ayarimatsui/Portable_Drinkbar/raspi-case-CAD/base_of_base.SLDPRT

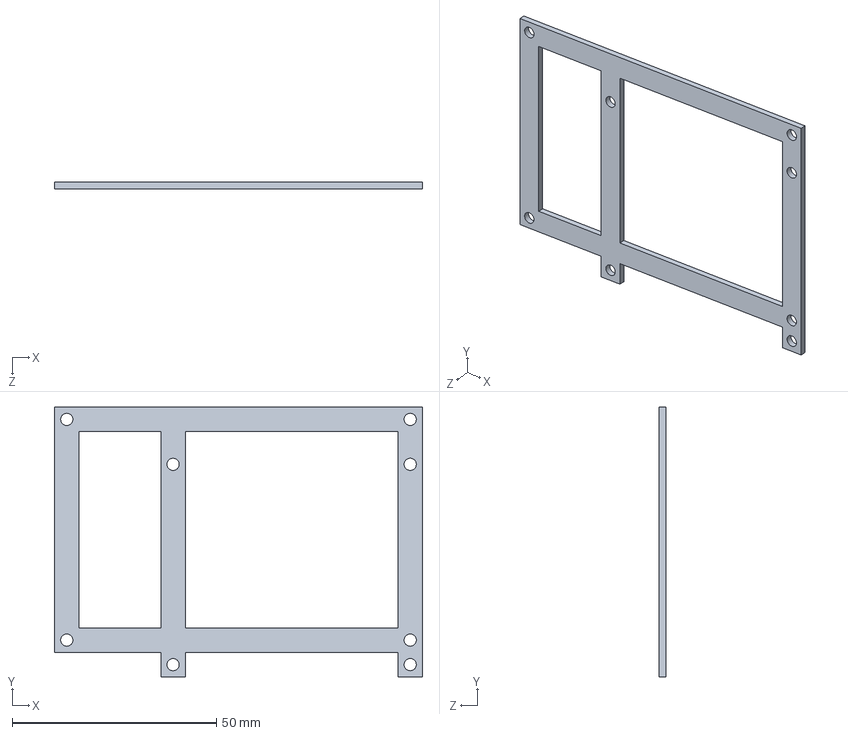
[picture p26: CAD file, 2020-01-28]
raspi-case-CAD/base_of_base.SLDPRT
90.0 x 66.0 x 1.60 mm
