ayarimatsui/Portable_Drinkbar/make_aroma/CAD_data/aroma-maker-CAD/cover/parts/cover_top.SLDPRT

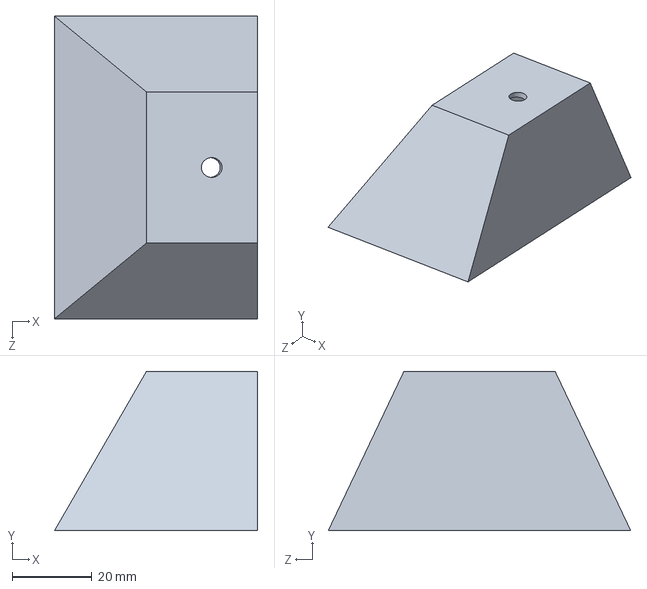
[picture p27: CAD file, 2019-12-03]
make_aroma/CAD_data/aroma-maker-CAD/cover/parts/cover_top.SLDPRT
51.0 x 40.0 x 76.0 mm
