ayarimatsui/Portable_Drinkbar/make_aroma/CAD_data/aroma-maker-CAD/main/parts/pin.SLDPRT

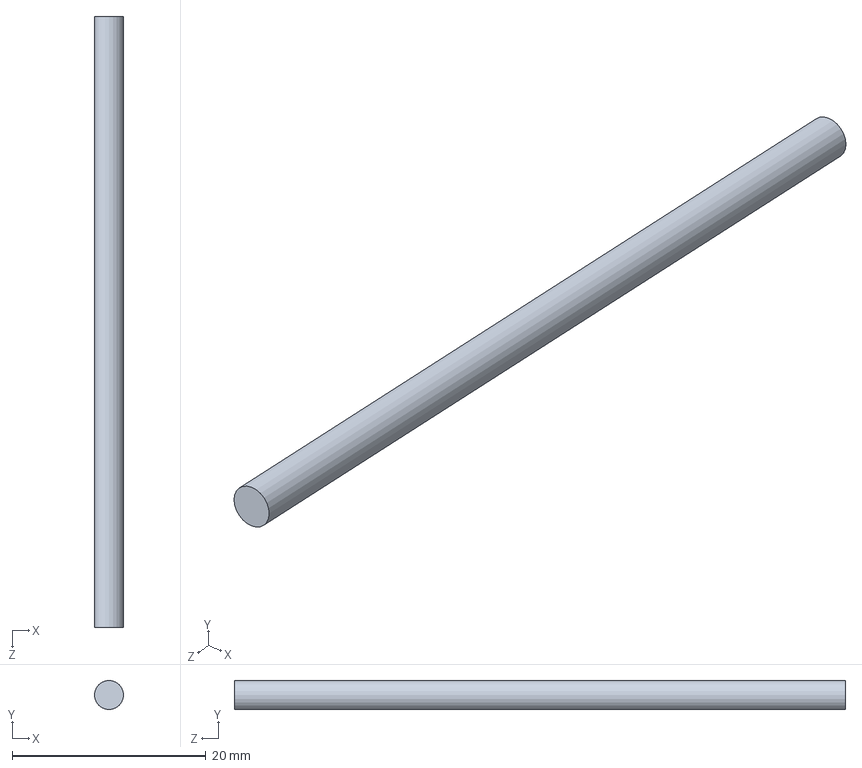
[picture p28: CAD file, 2019-12-03]
make_aroma/CAD_data/aroma-maker-CAD/main/parts/pin.SLDPRT
3.00 x 3.00 x 63.0 mm
