ayarimatsui/Portable_Drinkbar/make_aroma/CAD_data/aroma-maker-CAD/cover/parts/cover_bottom.SLDPRT

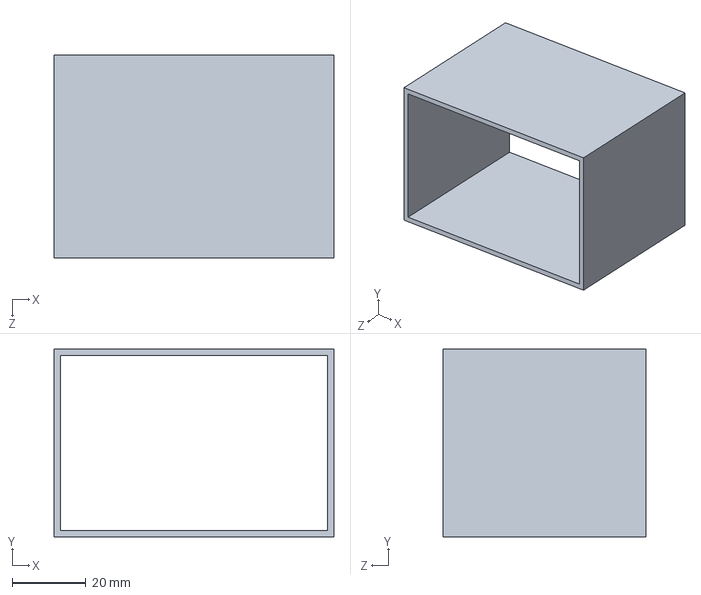
[picture p29: CAD file, 2019-12-03]
make_aroma/CAD_data/aroma-maker-CAD/cover/parts/cover_bottom.SLDPRT
76.0 x 51.0 x 55.0 mm
