ayarimatsui/Portable_Drinkbar/make_aroma/CAD_data/aroma-maker-CAD/main/parts/cotton-container.SLDPRT

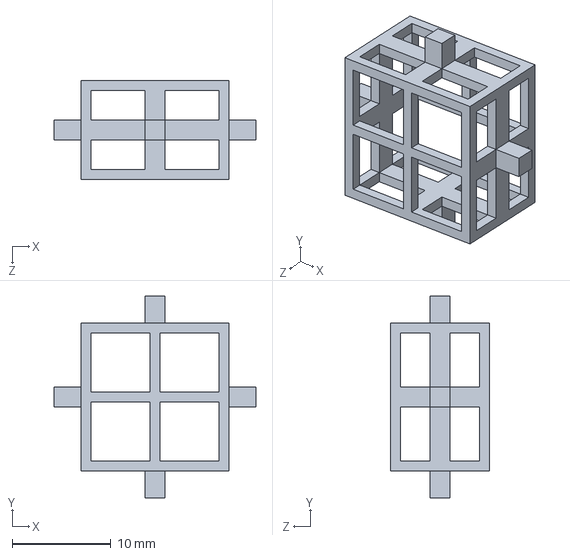
[picture p30: CAD file, 2019-12-03]
make_aroma/CAD_data/aroma-maker-CAD/main/parts/cotton-container.SLDPRT
20.5 x 20.5 x 10.0 mm
