ayarimatsui/Portable_Drinkbar/make_aroma/CAD_data/aroma-maker-CAD/cover/parts/extended_wall.SLDPRT

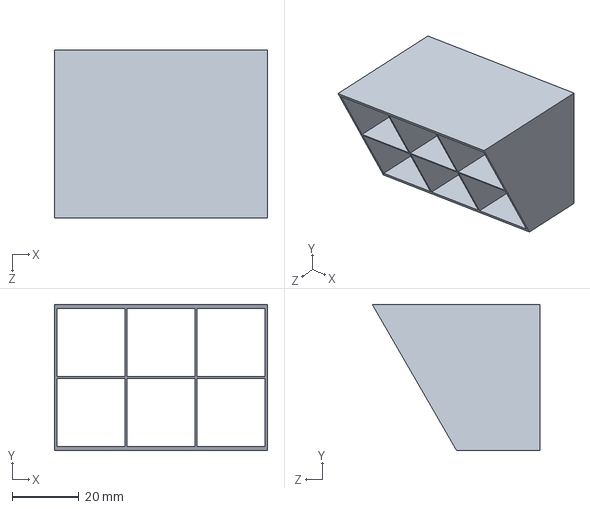
[picture p31: CAD file, 2019-12-03]
make_aroma/CAD_data/aroma-maker-CAD/cover/parts/extended_wall.SLDPRT
64.0 x 44.0 x 50.4 mm
