ayarimatsui/Portable_Drinkbar/raspi-case-CAD/case6.SLDPRT

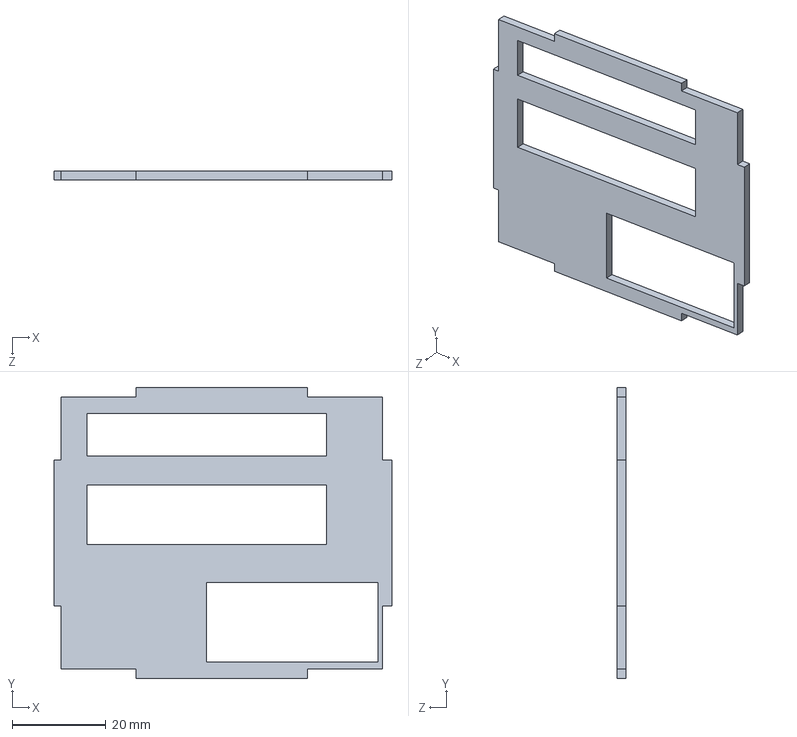
[picture p32: CAD file, 2020-01-28]
raspi-case-CAD/case6.SLDPRT
72.0 x 62.0 x 2.00 mm
