ayarimatsui/Portable_Drinkbar/raspi-case-CAD/plates=base.SLDPRT

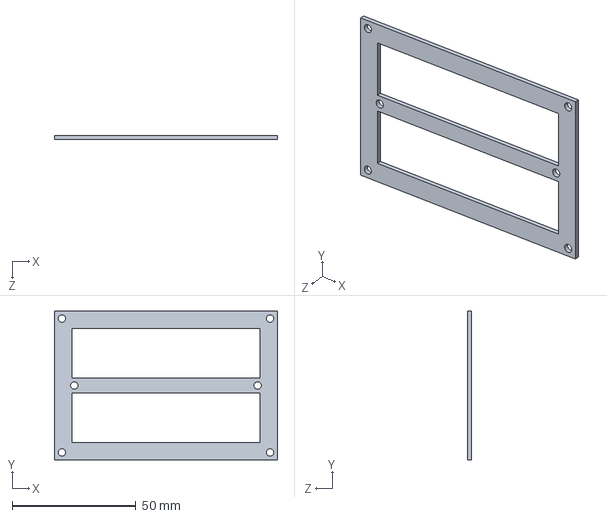
[picture p33: CAD file, 2020-01-28]
raspi-case-CAD/plates=base.SLDPRT
90.0 x 60.0 x 1.60 mm
