ayarimatsui/Portable_Drinkbar/raspi-case-CAD/case5.SLDPRT

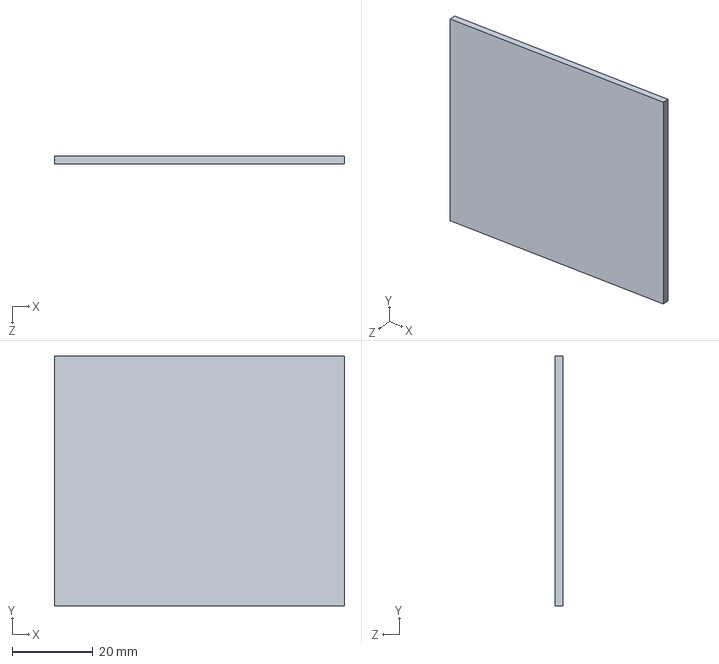
[picture p34: CAD file, 2020-01-28]
raspi-case-CAD/case5.SLDPRT
72.0 x 62.0 x 2.00 mm
