ayarimatsui/Portable_Drinkbar/raspi-case-CAD/pin_3x25.SLDPRT

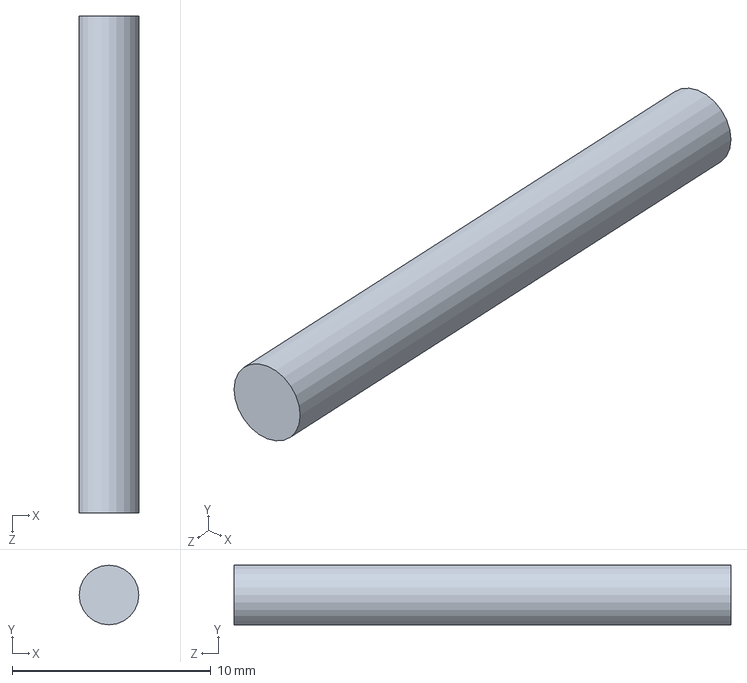
[picture p35: CAD file, 2020-01-28]
raspi-case-CAD/pin_3x25.SLDPRT
3.00 x 3.00 x 25.0 mm
