ayarimatsui/Portable_Drinkbar/raspi-case-CAD/case1.SLDPRT

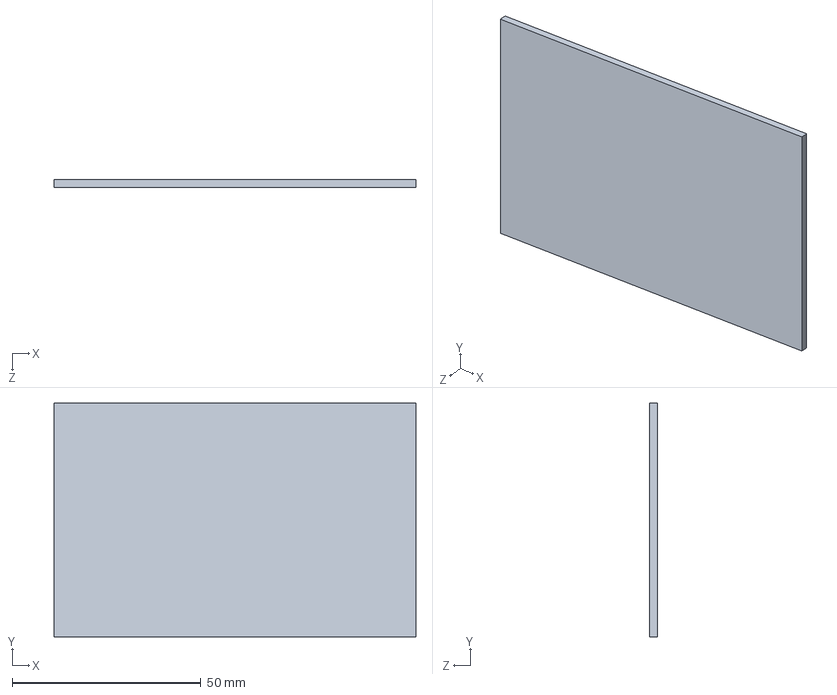
[picture p36: CAD file, 2020-01-28]
raspi-case-CAD/case1.SLDPRT
96.0 x 62.0 x 2.00 mm
