ayarimatsui/Portable_Drinkbar/make_color/run_from_here/apple_juice.py

#!/usr/bin/env python3
# NeoPixel library strandtest example
# Author: Tony DiCola (tony@tonydicola.com)
#
# Direct port of the Arduino NeoPixel library strandtest example.  Showcases
# various animations on a strip of NeoPixels.

import time
from neopixel import *
import argparse

# LED strip configuration:
LED_COUNT1     = 24     # Number of LED pixels.
LED_COUNT2     = 7
LED_PIN1       = 21      # GPIO pin connected to the pixels (18 uses PWM!).
LED_PIN2       = 10
#LED_PIN        = 10      # GPIO pin connected to the pixels (10 uses SPI /dev/spidev0.0).
LED_FREQ_HZ    = 800000  # LED signal frequency in hertz (usually 800khz)
LED_DMA        = 10      # DMA channel to use for generating signal (try 10)
LED_BRIGHTNESS = 200     # Set to 0 for darkest and 255 for brightest
LED_INVERT     = False   # True to invert the signal (when using NPN transistor level shift)
LED_CHANNEL    = 0       # set to '1' for GPIOs 13, 19, 41, 45 or 53



# Define functions which animate LEDs in various ways.
def colorWipe(strip, color, wait_ms=50):
    """Wipe color across display a pixel at a time."""
    for i in range(strip.numPixels()):
        strip.setPixelColor(i, color)
        strip.show()
        time.sleep(wait_ms/1000.0)
        
def show_color(strip, color, wait_ms=50):
    """Wipe color across display a pixel at a time."""
    for i in range(strip.numPixels()):
        strip.setPixelColor(i, color)
        strip.show()
        #time.sleep(wait_ms/1000.0)


# Main program logic follows:
if __name__ == '__main__':
    # Process arguments
    parser = argparse.ArgumentParser()
    parser.add_argument('-c', '--clear', action='store_true', help='clear the display on exit')
    args = parser.parse_args()

    # Create NeoPixel object with appropriate configuration.
    strip1 = Adafruit_NeoPixel(LED_COUNT1, LED_PIN1, LED_FREQ_HZ, LED_DMA, LED_INVERT, LED_BRIGHTNESS, LED_CHANNEL)
    strip2 = Adafruit_NeoPixel(LED_COUNT2, LED_PIN2, LED_FREQ_HZ, LED_DMA, LED_INVERT, LED_BRIGHTNESS, LED_CHANNEL)
    # Intialize the library (must be called once before other functions).
    strip1.begin()
    strip2.begin()
    
    print ('Press Ctrl-C to quit.')
    if not args.clear:
        print('Use "-c" argument to clear LEDs on exit')

    try:
        print("init")
        colorWipe(strip1, Color(200, 240, 40))  # wipe
        colorWipe(strip2, Color(200, 240, 40))  # wipe
        while True:
            show_color(strip1, Color(200, 240, 40))
            show_color(strip2, Color(200, 240, 40))
            

    except KeyboardInterrupt:
        if args.clear:
            colorWipe(strip, Color(0,0,0), 10)
