ayarimatsui/Portable_Drinkbar/make_aroma/sample/switch_fan.py

# -*- coding: utf-8 -*-
import RPi.GPIO as GPIO
import time
import threading

# GPIO定義
fan1_pin=15
fan2_pin=18
fan3_pin=20
fan4_pin=26
fan5_pin=12
fan6_pin=16

# すべてのファンがoffのとき0、1~4のときはその番号のファンが回る
switch=0

# 別スレッドを立てて入力を取得
print("0 -> off all fans")
print("1 -> turn on fan1")
print("2 -> turn on fan2")
print("3 -> turn on fan3")
print("4 -> turn on fan4")
print("5 -> turn on fan5")
print("6 -> turn on fan6")

def wait_input():
    global switch
    key=input()
    if key=="0":
        switch=0
    elif key=="1":
        switch=1
    elif key=="2":
        switch=2
    elif key=="3":
        switch=3
    elif key=="4":
        switch=4
    elif key=="5":
        switch=5
    elif key=="6":
        switch=6
    print(switch)
    #print("on_off = "+str(on_off))

#th = threading.Thread(target=wait_input)
#th.start()

# GPIO初期化
GPIO.setmode(GPIO.BCM)
GPIO.setup(fan1_pin, GPIO.OUT)
GPIO.setup(fan2_pin, GPIO.OUT)
GPIO.setup(fan3_pin, GPIO.OUT)
GPIO.setup(fan4_pin, GPIO.OUT)
GPIO.setup(fan5_pin, GPIO.OUT)
GPIO.setup(fan6_pin, GPIO.OUT)

try:
    while True:
        th = threading.Thread(target=wait_input)
        th.start()
        if switch==0:
            GPIO.output(fan1_pin,GPIO.LOW)
            GPIO.output(fan2_pin,GPIO.LOW)
            GPIO.output(fan3_pin,GPIO.LOW)
            GPIO.output(fan4_pin,GPIO.LOW)
            GPIO.output(fan5_pin,GPIO.LOW)
            GPIO.output(fan6_pin,GPIO.LOW)
        elif switch==1:
            GPIO.output(fan1_pin,GPIO.HIGH)
            GPIO.output(fan2_pin,GPIO.LOW)
            GPIO.output(fan3_pin,GPIO.LOW)
            GPIO.output(fan4_pin,GPIO.LOW)
            GPIO.output(fan5_pin,GPIO.LOW)
            GPIO.output(fan6_pin,GPIO.LOW)
        elif switch==2:
            GPIO.output(fan1_pin,GPIO.LOW)
            GPIO.output(fan2_pin,GPIO.HIGH)
            GPIO.output(fan3_pin,GPIO.LOW)
            GPIO.output(fan4_pin,GPIO.LOW)
            GPIO.output(fan5_pin,GPIO.LOW)
            GPIO.output(fan6_pin,GPIO.LOW)
        elif switch==3:
            GPIO.output(fan1_pin,GPIO.LOW)
            GPIO.output(fan2_pin,GPIO.LOW)
            GPIO.output(fan3_pin,GPIO.HIGH)
            GPIO.output(fan4_pin,GPIO.LOW)
            GPIO.output(fan5_pin,GPIO.LOW)
            GPIO.output(fan6_pin,GPIO.LOW)
        elif switch==4:
            GPIO.output(fan1_pin,GPIO.LOW)
            GPIO.output(fan2_pin,GPIO.LOW)
            GPIO.output(fan3_pin,GPIO.LOW)
            GPIO.output(fan4_pin,GPIO.HIGH)
            GPIO.output(fan5_pin,GPIO.LOW)
            GPIO.output(fan6_pin,GPIO.LOW)
        elif switch==5:
            GPIO.output(fan1_pin,GPIO.LOW)
            GPIO.output(fan2_pin,GPIO.LOW)
            GPIO.output(fan3_pin,GPIO.LOW)
            GPIO.output(fan4_pin,GPIO.LOW)
            GPIO.output(fan5_pin,GPIO.HIGH)
            GPIO.output(fan6_pin,GPIO.LOW)
        elif switch==6:
            GPIO.output(fan1_pin,GPIO.LOW)
            GPIO.output(fan2_pin,GPIO.LOW)
            GPIO.output(fan3_pin,GPIO.LOW)
            GPIO.output(fan4_pin,GPIO.LOW)
            GPIO.output(fan5_pin,GPIO.LOW)
            GPIO.output(fan6_pin,GPIO.HIGH)
        time.sleep(0.3)

except KeyboardInterrupt:
    pass

finally:
   print("clean up") 
   GPIO.cleanup()
   
th.join()
